ProMad24/WRO-Future-Engineers-2025/Team Photos/Funny Photo.jpg

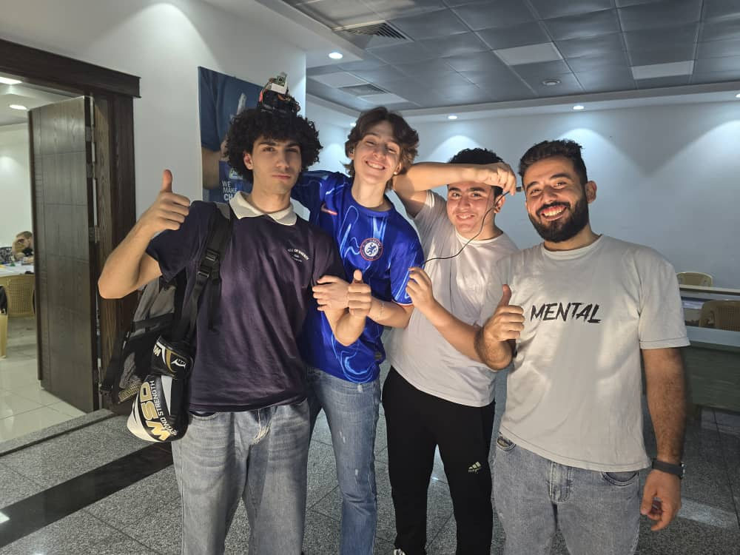
Team Photos/Funny Photo.jpg
