ProMad24/WRO-Future-Engineers-2025/Team Photos/Official Photo.jpg

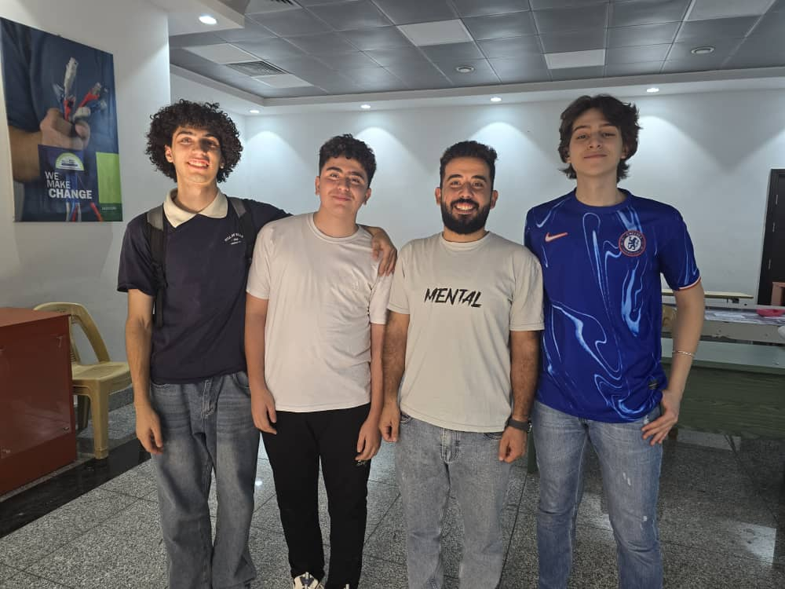
Team Photos/Official Photo.jpg
