ProMad24/WRO-Future-Engineers-2025/Vehicle Photos/V-Above.jpg

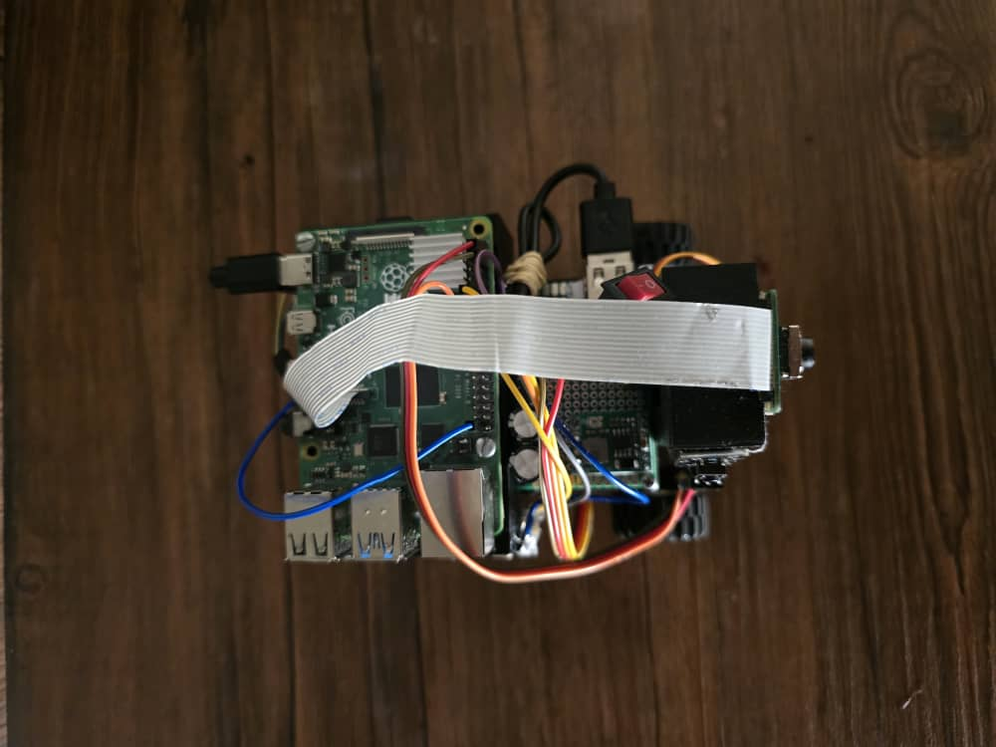
Vehicle Photos/V-Above.jpg
