ProMad24/WRO-Future-Engineers-2025/Vehicle Photos/V-Behind.jpg

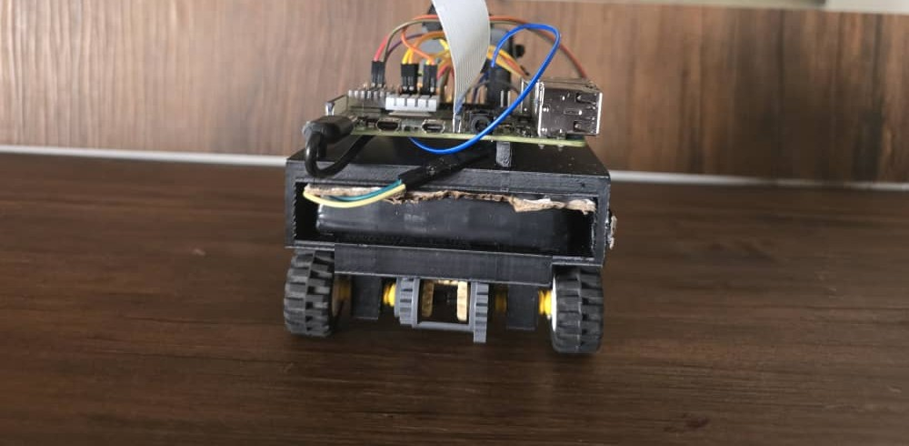
Vehicle Photos/V-Behind.jpg
