ProMad24/WRO-Future-Engineers-2025/Vehicle Photos/V-Front.jpg

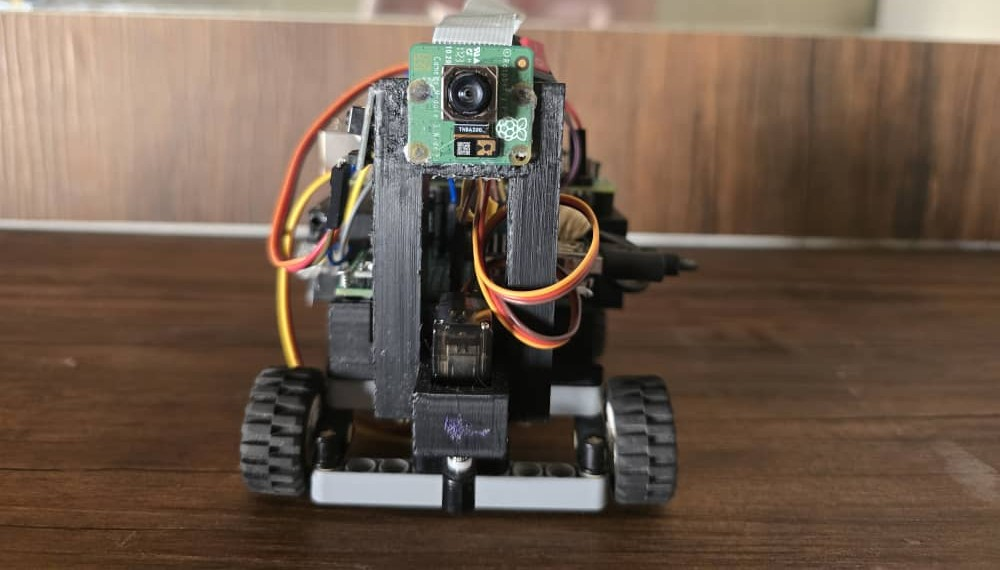
Vehicle Photos/V-Front.jpg
