ProMad24/WRO-Future-Engineers-2025/Vehicle Photos/V-Left.jpg

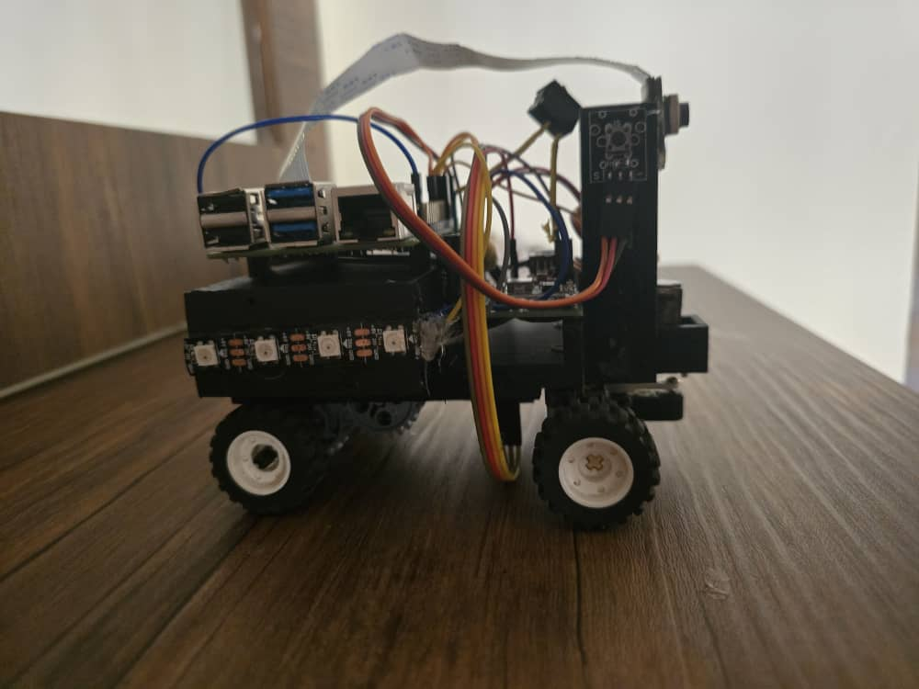
Vehicle Photos/V-Left.jpg
