ProMad24/WRO-Future-Engineers-2025/Vehicle Photos/V-Under.jpg

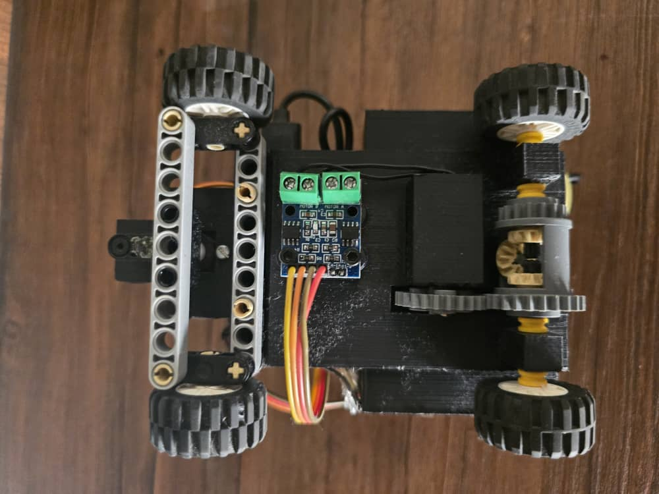
Vehicle Photos/V-Under.jpg
