ProMad24/WRO-Future-Engineers-2025/Schemes and Electromechanical Components/470uf 25V Capacitor.png

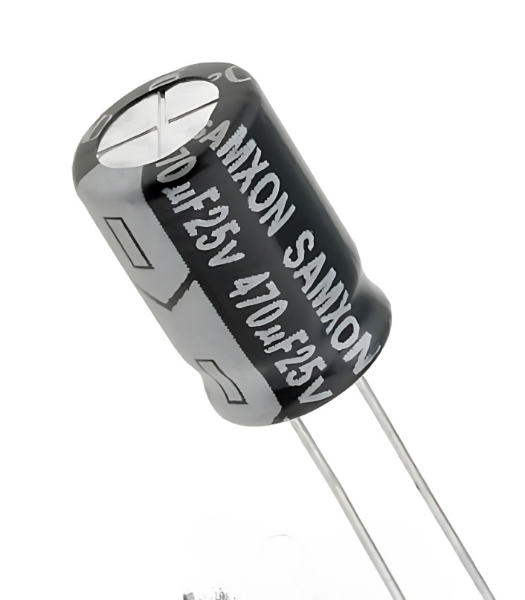
Schemes and Electromechanical Components/470uf 25V Capacitor.png
