ProMad24/WRO-Future-Engineers-2025/Schemes and Electromechanical Components/G12-N20 Geared Mini DC Motor.png

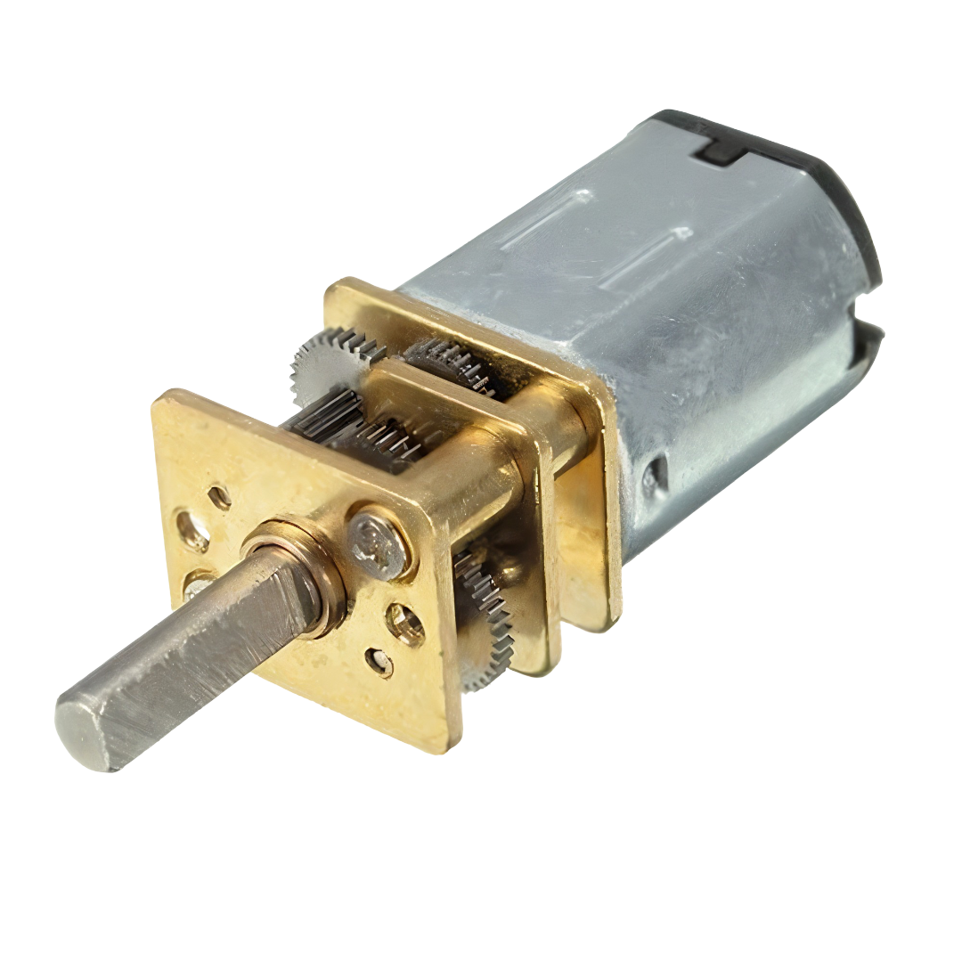
Schemes and Electromechanical Components/G12-N20 Geared Mini DC Motor.png
