ProMad24/WRO-Future-Engineers-2025/Schemes and Electromechanical Components/MG90s Mini Servo Motor.jpg

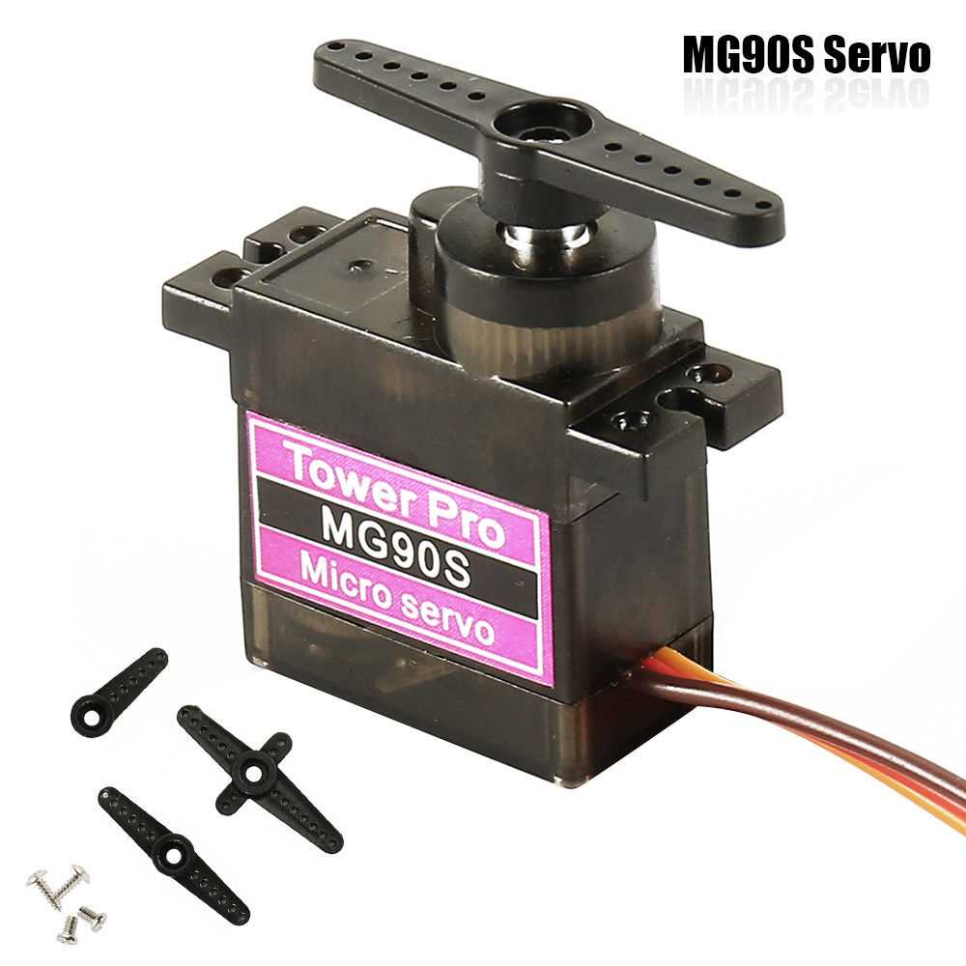
Schemes and Electromechanical Components/MG90s Mini Servo Motor.jpg
