ProMad24/WRO-Future-Engineers-2025/Schemes and Electromechanical Components/Mini-360 DC-DC Buck Converter.jpg

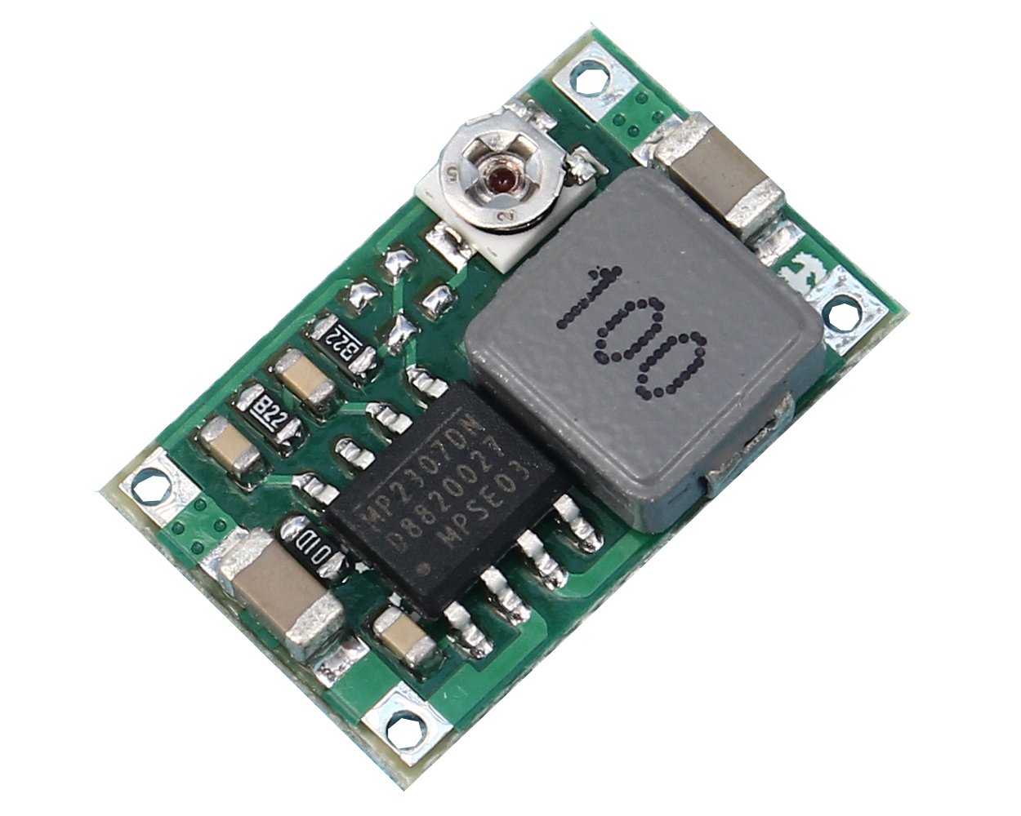
Schemes and Electromechanical Components/Mini-360 DC-DC Buck Converter.jpg
