ProMad24/WRO-Future-Engineers-2025/Schemes and Electromechanical Components/Push Button.png

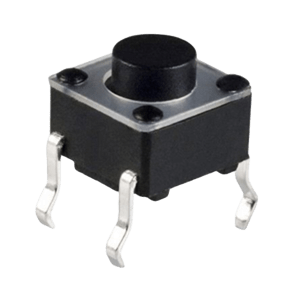
Schemes and Electromechanical Components/Push Button.png
