ProMad24/WRO-Future-Engineers-2025/Schemes and Electromechanical Components/Raspberry Pi 4 Model B.png

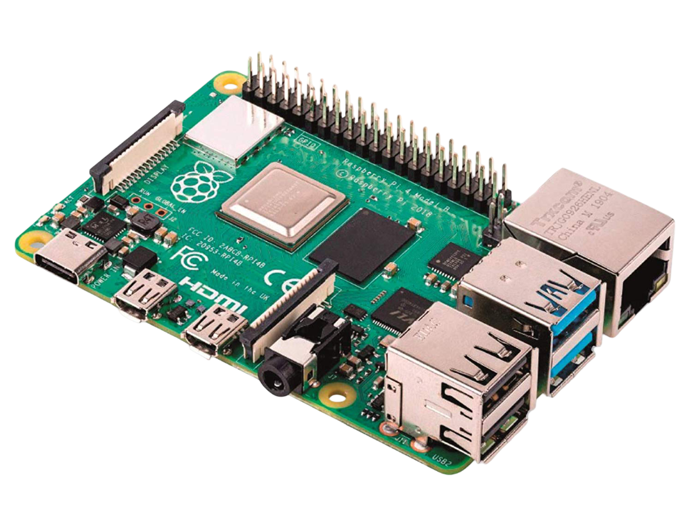
Schemes and Electromechanical Components/Raspberry Pi 4 Model B.png
