ProMad24/WRO-Future-Engineers-2025/Schemes and Electromechanical Components/Raspberry Pi Camera Module 3.png

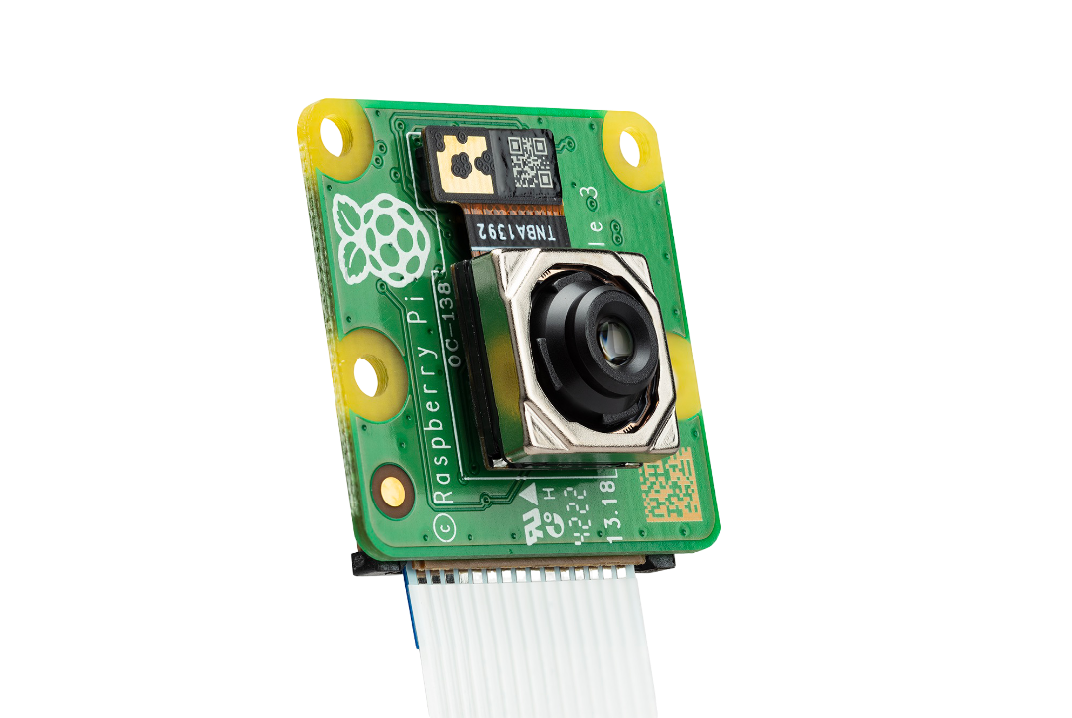
Schemes and Electromechanical Components/Raspberry Pi Camera Module 3.png
