ProMad24/WRO-Future-Engineers-2025/Schemes and Electromechanical Components/Switch.webp

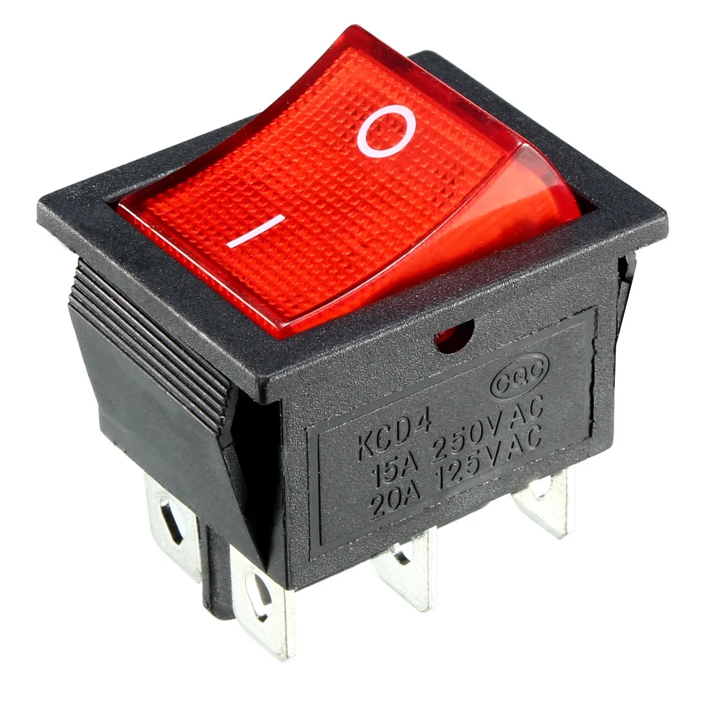
Schemes and Electromechanical Components/Switch.webp
