ProMad24/WRO-Future-Engineers-2025/Schemes and Electromechanical Components/USB DC to DC Converter.webp

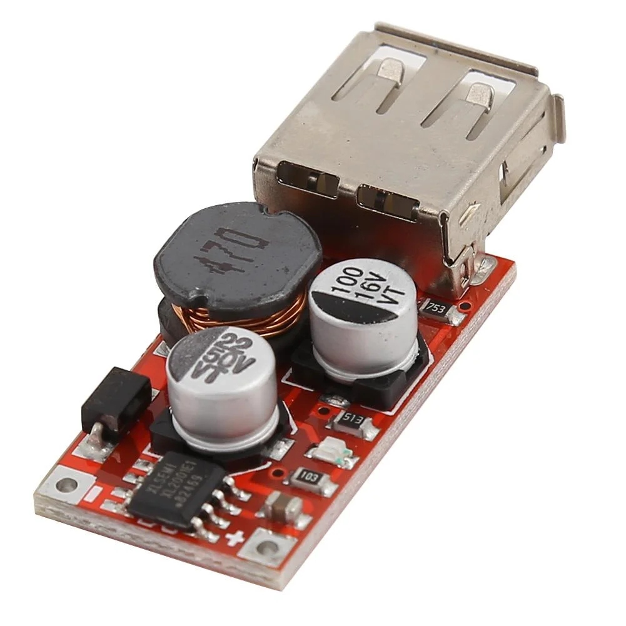
Schemes and Electromechanical Components/USB DC to DC Converter.webp
