ProMad24/WRO-Future-Engineers-2025/Schemes and Electromechanical Components/Wiring Diagram.png

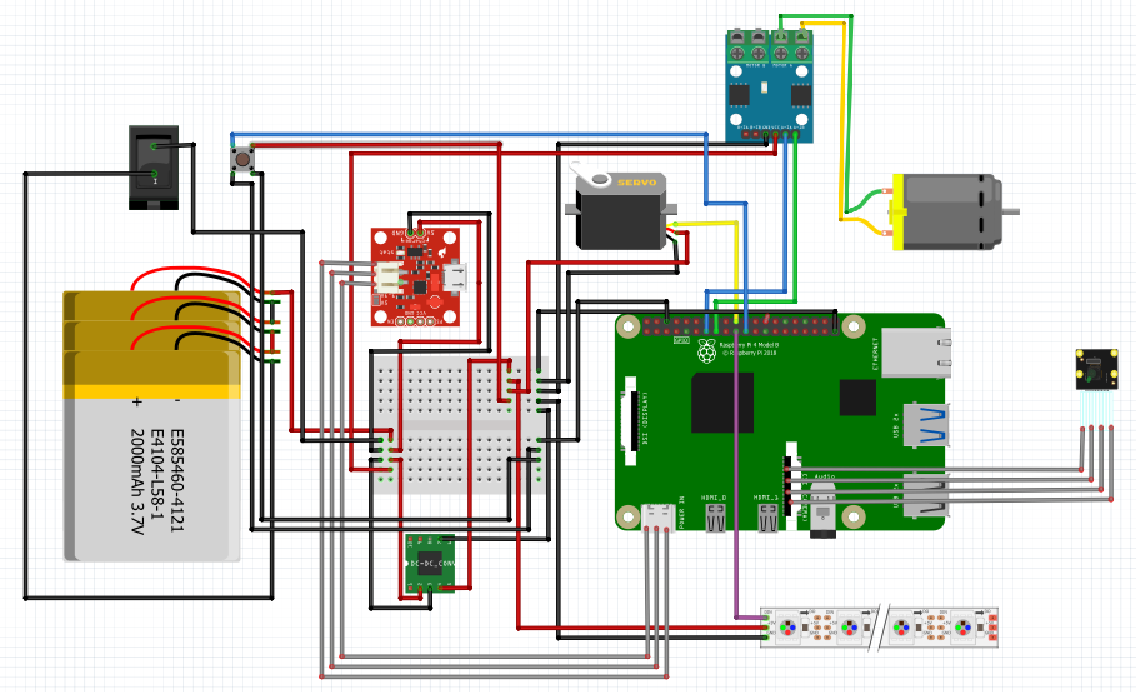
Schemes and Electromechanical Components/Wiring Diagram.png
